jsandmeyer/camaro-aftermarket-radio-aux-display-rp2350/src/util/OLED.h

#ifndef CAMARO_DISPLAY_OLED_H
#define CAMARO_DISPLAY_OLED_H

// OLED display measurements
#define SCREEN_WIDTH 128
#define SCREEN_HEIGHT 32

#define OLED_SPI_BAUD 1000000UL

#define OLED_RX 8 // 11
#define OLED_CS 9 // 12
#define OLED_SCK 10 // 14
#define OLED_TX 11 // 15

#define OLED_RST 12 // 16
#define OLED_DC 13 // 17
#define SPI_CS_PIN_OLED 14 // 19

#endif //CAMARO_DISPLAY_OLED_H
