jsandmeyer/camaro-aftermarket-radio-aux-display-rp2350/src/util/GMLan.h

#ifndef GMLAN_H
#define GMLAN_H

#include <RP2350Wrapper.h>

// constants for GMLAN message masking & shifting
#define GMLAN_PRI_MASK 0x1C000000 // priority is first 3 bits
#define GMLAN_PRI_SHIFT 0x1A // shift priority right 1A (26) bits, for example 0b1110101... becomes 0b111
#define GMLAN_ARB_MASK 0x03FFE000 // target arb id is next 13 bits
#define GMLAN_ARB_SHIFT 0x0D // shift target arb id right 0D (13) bits
#define GMLAN_SND_MASK 0x00001FFF // sender arb id is last 13 bits
#define GMLAN_SND_SHIFT 0x00 // no need to shift sender arb id

// helper macros to shift/decipher GMLAN messages
#define GMLAN_MASK_AND_SHIFT(v, m, s) ((v & m) >> s)
#define GMLAN_PRI(v) GMLAN_MASK_AND_SHIFT(v, GMLAN_PRI_MASK, GMLAN_PRI_SHIFT)
#define GMLAN_ARB(v) GMLAN_MASK_AND_SHIFT(v, GMLAN_ARB_MASK, GMLAN_ARB_SHIFT)
#define GMLAN_SND(v) GMLAN_MASK_AND_SHIFT(v, GMLAN_SND_MASK, GMLAN_SND_SHIFT)

// helper macros to build GMLAN masks or messages from parts
#define GMLAN_UNSHIFT_AND_MASK(v, m, s) ((v << s) & m)
#define GMLAN_R_PRI(v) GMLAN_UNSHIFT_AND_MASK(v, GMLAN_PRI_MASK, GMLAN_PRI_SHIFT)
#define GMLAN_R_ARB(v) GMLAN_UNSHIFT_AND_MASK(v, GMLAN_ARB_MASK, GMLAN_ARB_SHIFT)
#define GMLAN_R_SND(v) GMLAN_UNSHIFT_AND_MASK(v, GMLAN_SND_MASK, GMLAN_SND_SHIFT)

// GMLAN Messages
// Rear Park Assist
#define GMLAN_MSG_PARK_ASSIST 0x1D4UL
// Outside Temperature
#define GMLAN_MSG_TEMPERATURE 0x212UL
// Cluster Units
#define GMLAN_MSG_CLUSTER_UNITS 0x425UL

// GMLAN Message Values
// Rear Park Assist
#define GMLAN_VAL_PARK_ASSIST_OFF 0x0F
#define GMLAN_VAL_PARK_ASSIST_ON 0x00
// Cluster Units
#define GMLAN_VAL_CLUSTER_UNITS_METRIC 0x00
#define GMLAN_VAL_CLUSTER_UNITS_IMPERIAL 0x05

#define GMLAN_CAN_BITRATE 33333UL
#define GMLAN_CAN_PIO 0
#define GMLAN_CAN_PIO_IRQn PIO0_IRQ_0_IRQn
#define GMLAN_CAN_PRI 1
#define GMLAN_CAN_RX 26
#define GMLAN_CAN_TX 27

#endif //GMLAN_H
